gonggr/Open-source-Multinuclear-Low-field-Pre-clinical-MRI-Scanner/RLC circuits/RLC circuits.jpg

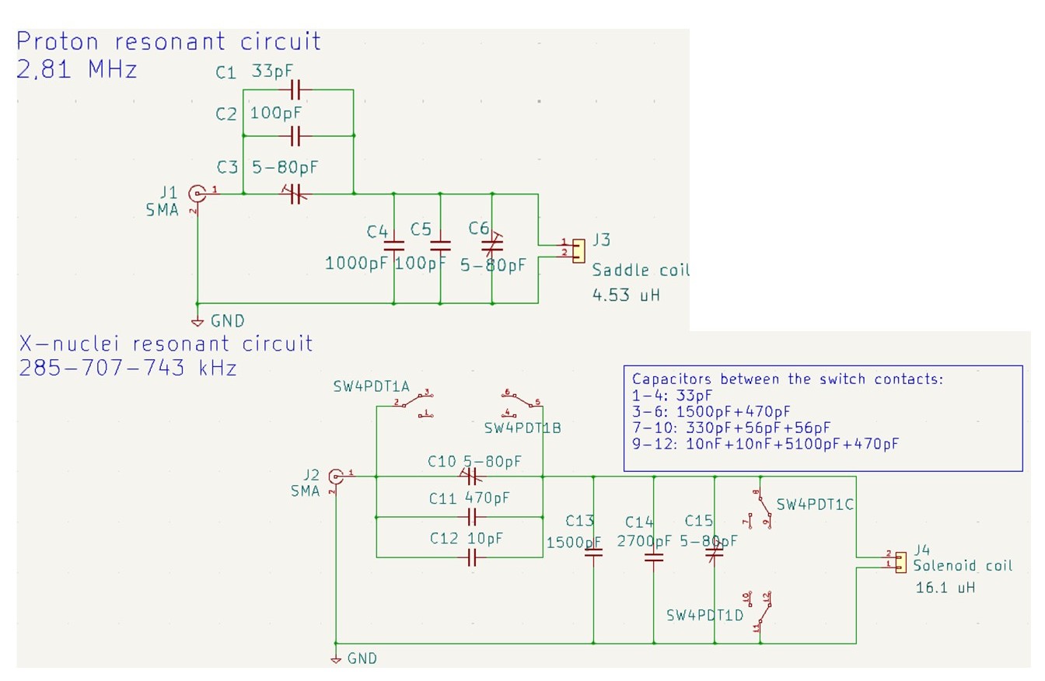
RLC circuits/RLC circuits.jpg
