gonggr/Open-source-Multinuclear-Low-field-Pre-clinical-MRI-Scanner/Magnet Assembling/20220909_121225.jpg

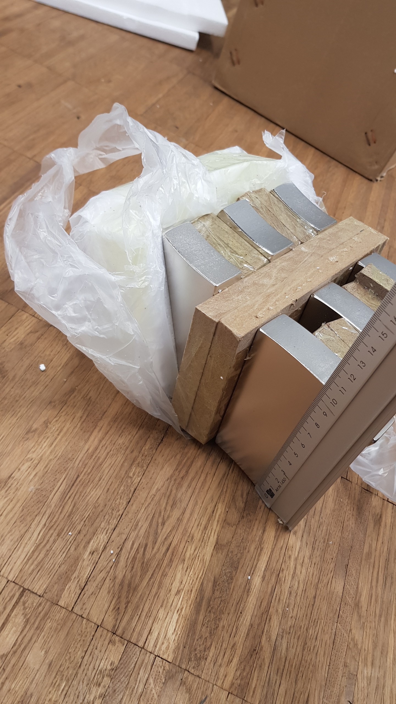
Magnet Assembling/20220909_121225.jpg
