gonggr/Open-source-Multinuclear-Low-field-Pre-clinical-MRI-Scanner/Magnet Assembling/20220919_095450.jpg

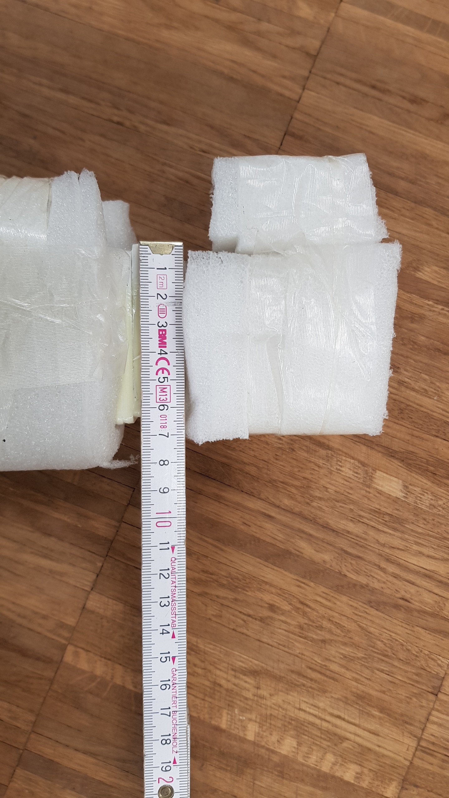
Magnet Assembling/20220919_095450.jpg
