gonggr/Open-source-Multinuclear-Low-field-Pre-clinical-MRI-Scanner/Magnet Assembling/20230217_094706.jpg

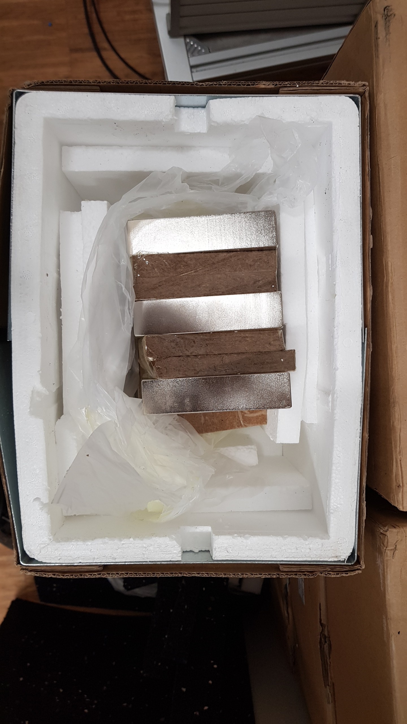
Magnet Assembling/20230217_094706.jpg
