gonggr/Open-source-Multinuclear-Low-field-Pre-clinical-MRI-Scanner/Magnet Assembling/20230221_135123.jpg

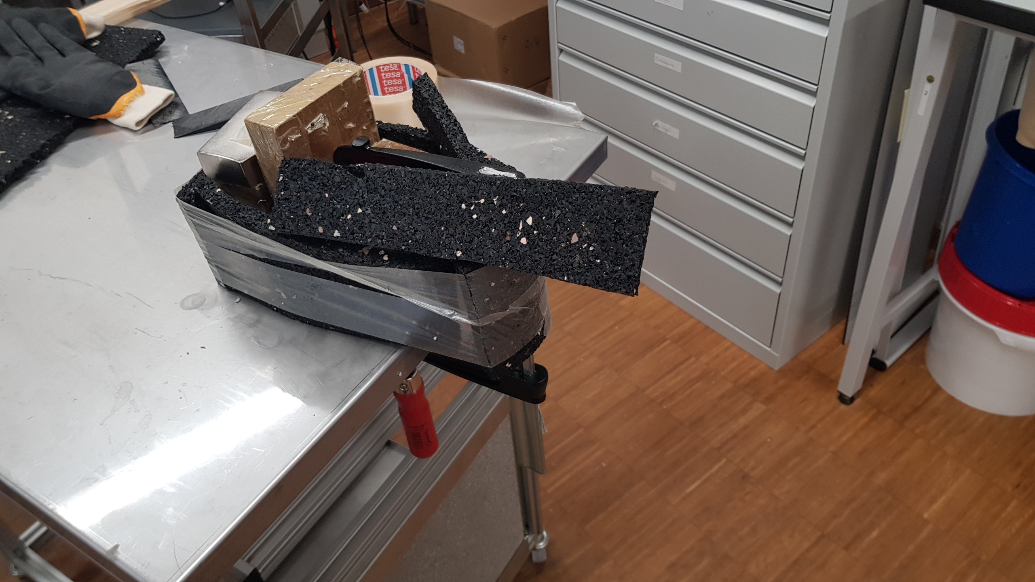
Magnet Assembling/20230221_135123.jpg
