gonggr/Open-source-Multinuclear-Low-field-Pre-clinical-MRI-Scanner/Magnet Assembling/20230221_140905.jpg

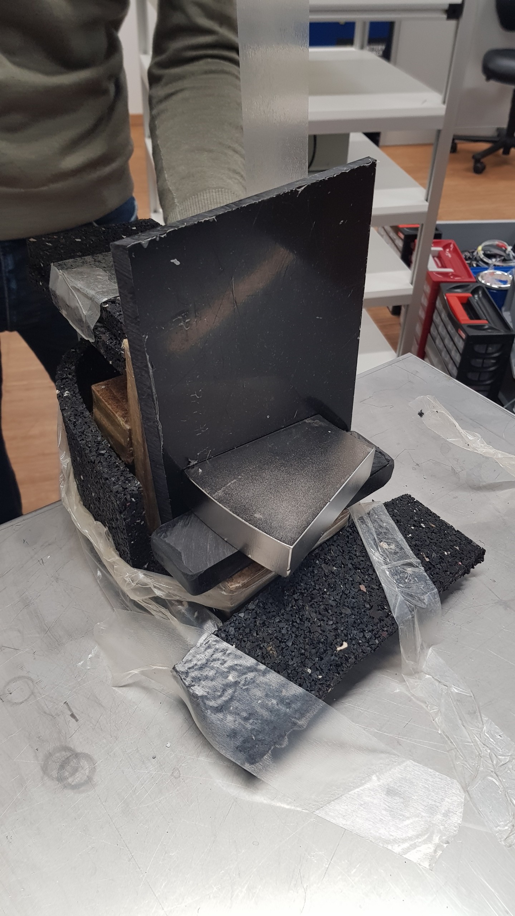
Magnet Assembling/20230221_140905.jpg
