gonggr/Open-source-Multinuclear-Low-field-Pre-clinical-MRI-Scanner/Magnet Assembling/20230221_140908.jpg

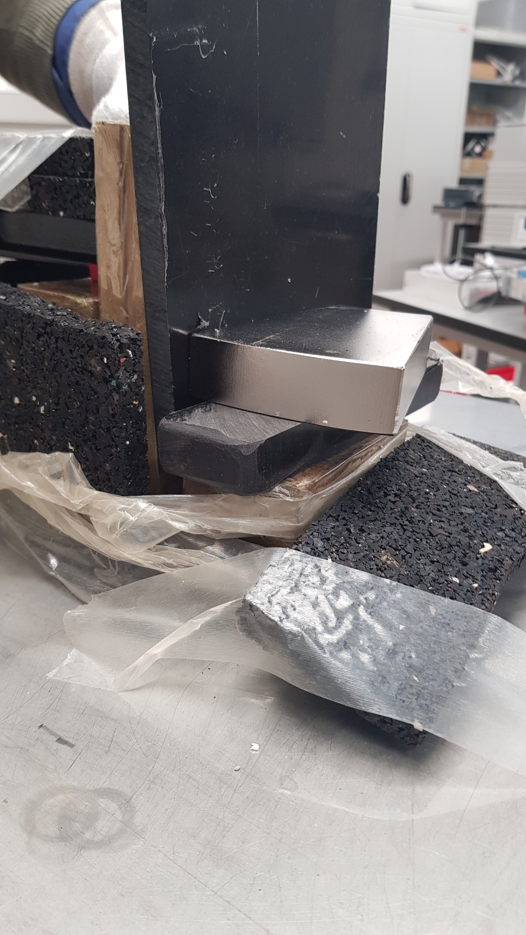
Magnet Assembling/20230221_140908.jpg
