gonggr/Open-source-Multinuclear-Low-field-Pre-clinical-MRI-Scanner/Magnet Assembling/20230221_142411.jpg

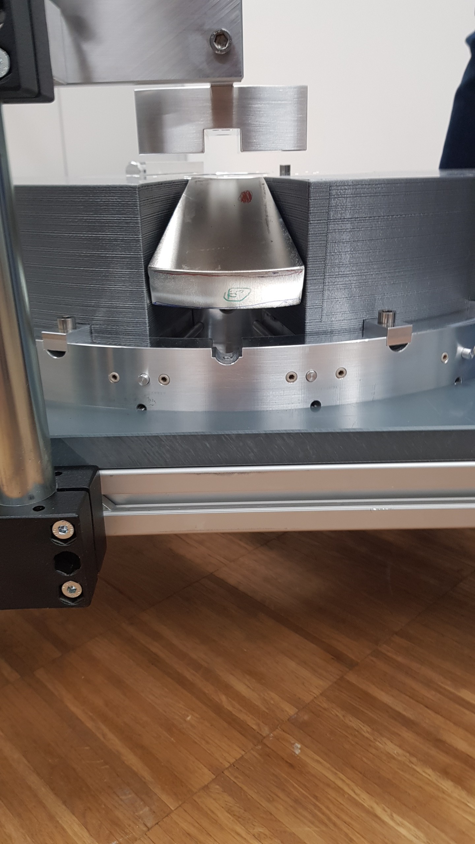
Magnet Assembling/20230221_142411.jpg
